sparkfun/SparkFun_Qwiic_9DoF_IMU_Breakout/Documentation/eMD/1.0.0/doc/libIDD/html/a00162.png

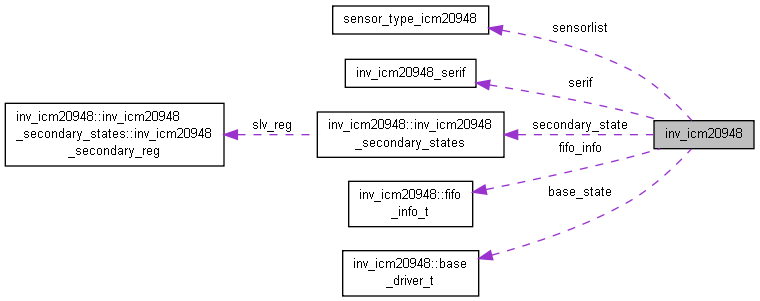
Documentation/eMD/1.0.0/doc/libIDD/html/a00162.png
