sparkfun/SparkFun_Qwiic_9DoF_IMU_Breakout/Documentation/eMD/1.0.0/doc/libIDD/html/graph_legend.png

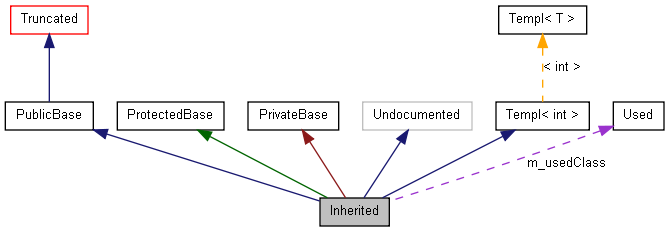
Documentation/eMD/1.0.0/doc/libIDD/html/graph_legend.png
