sparkfun/SparkFun_Qwiic_9DoF_IMU_Breakout/Documentation/eMD_SM/EMD-App/src/config/conf_board.h

/**
 * \file
 *
 * \brief Board configuration.
 *
 * Copyright (c) 2014-2015 Atmel Corporation. All rights reserved.
 *
 * \asf_license_start
 *
 * \page License
 *
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
 * 3. The name of Atmel may not be used to endorse or promote products derived
 *    from this software without specific prior written permission.
 *
 * 4. This software may only be redistributed and used in connection with an
 *    Atmel microcontroller product.
 *
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
 * \asf_license_stop
 *
 */
/*
 * Support and FAQ: visit <a href="http://www.atmel.com/design-support/">Atmel Support</a>
 */

#ifndef CONF_BOARD_H_INCLUDED
#define CONF_BOARD_H_INCLUDED

#ifndef CONF_BOARD_USART0
#define CONF_BOARD_USART0
#endif

#ifndef CONF_BOARD_UART_CONSOLE
#define CONF_BOARD_UART_CONSOLE
#endif

#ifndef BOARD_FLEXCOM_SPI
/** FLEXCOM base address for SPI mode*/
#define BOARD_FLEXCOM_SPI    FLEXCOM5
#endif

#ifndef BOARD_FLEXCOM_USART
/** FLEXCOM base address for USART mode*/
#define BOARD_FLEXCOM_USART  FLEXCOM6
#endif

/* I2C defines - I2C_FLAG */

/** Configure TWI4 pins */
#define CONF_BOARD_TWI4

/** TWI Bus Clock 400kHz */
#define TWI_CLK					400000

/** Flexcom application to use */
#define BOARD_FLEXCOM_TWI		FLEXCOM4

/** TWI ID for simulated EEPROM application to use */
#define BOARD_ID_TWI			ID_TWI4

/** TWI Base for simulated TWI EEPROM application to use */
#define BOARD_BASE_TWI			TWI4

/** SPI MACRO definition */
#define CONF_BOARD_SPI

/** SPI slave select MACRO definition */
#define CONF_BOARD_SPI_NPCS0
#define CONF_BOARD_SPI_NPCS1

/** Spi Hw ID . */
#define SPI_ID				ID_SPI5

/** SPI base address for SPI master mode*/
#define SPI_MASTER_BASE      SPI5
/** SPI base address for SPI slave mode, (on different board) */
#define SPI_SLAVE_BASE       SPI5
/** FLEXCOM base address for SPI mode*/
#define BOARD_FLEXCOM_SPI    FLEXCOM5

#endif /* CONF_BOARD_H_INCLUDED */
